AhmadGon/Advanced-Digital-Oscilloscope/Nios_SDRAM_COM/synthesis/submodules/Nios_SDRAM_COM_mm_interconnect_0_router.sv

// (C) 2001-2018 Intel Corporation. All rights reserved.
// Your use of Intel Corporation's design tools, logic functions and other 
// software and tools, and its AMPP partner logic functions, and any output 
// files from any of the foregoing (including device programming or simulation 
// files), and any associated documentation or information are expressly subject 
// to the terms and conditions of the Intel Program License Subscription 
// Agreement, Intel FPGA IP License Agreement, or other applicable 
// license agreement, including, without limitation, that your use is for the 
// sole purpose of programming logic devices manufactured by Intel and sold by 
// Intel or its authorized distributors.  Please refer to the applicable 
// agreement for further details.



// Your use of Altera Corporation's design tools, logic functions and other 
// software and tools, and its AMPP partner logic functions, and any output 
// files any of the foregoing (including device programming or simulation 
// files), and any associated documentation or information are expressly subject 
// to the terms and conditions of the Altera Program License Subscription 
// Agreement, Altera MegaCore Function License Agreement, or other applicable 
// license agreement, including, without limitation, that your use is for the 
// sole purpose of programming logic devices manufactured by Altera and sold by 
// Altera or its authorized distributors.  Please refer to the applicable 
// agreement for further details.


// $Id: //acds/rel/18.0std/ip/merlin/altera_merlin_router/altera_merlin_router.sv.terp#1 $
// $Revision: #1 $
// $Date: 2018/01/31 $
// $Author: psgswbuild $

// -------------------------------------------------------
// Merlin Router
//
// Asserts the appropriate one-hot encoded channel based on 
// either (a) the address or (b) the dest id. The DECODER_TYPE
// parameter controls this behaviour. 0 means address decoder,
// 1 means dest id decoder.
//
// In the case of (a), it also sets the destination id.
// -------------------------------------------------------

`timescale 1 ns / 1 ns

module Nios_SDRAM_COM_mm_interconnect_0_router_default_decode
  #(
     parameter DEFAULT_CHANNEL = 4,
               DEFAULT_WR_CHANNEL = -1,
               DEFAULT_RD_CHANNEL = -1,
               DEFAULT_DESTID = 5 
   )
  (output [81 - 79 : 0] default_destination_id,
   output [8-1 : 0] default_wr_channel,
   output [8-1 : 0] default_rd_channel,
   output [8-1 : 0] default_src_channel
  );

  assign default_destination_id = 
    DEFAULT_DESTID[81 - 79 : 0];

  generate
    if (DEFAULT_CHANNEL == -1) begin : no_default_channel_assignment
      assign default_src_channel = '0;
    end
    else begin : default_channel_assignment
      assign default_src_channel = 8'b1 << DEFAULT_CHANNEL;
    end
  endgenerate

  generate
    if (DEFAULT_RD_CHANNEL == -1) begin : no_default_rw_channel_assignment
      assign default_wr_channel = '0;
      assign default_rd_channel = '0;
    end
    else begin : default_rw_channel_assignment
      assign default_wr_channel = 8'b1 << DEFAULT_WR_CHANNEL;
      assign default_rd_channel = 8'b1 << DEFAULT_RD_CHANNEL;
    end
  endgenerate

endmodule


module Nios_SDRAM_COM_mm_interconnect_0_router
(
    // -------------------
    // Clock & Reset
    // -------------------
    input clk,
    input reset,

    // -------------------
    // Command Sink (Input)
    // -------------------
    input                       sink_valid,
    input  [95-1 : 0]    sink_data,
    input                       sink_startofpacket,
    input                       sink_endofpacket,
    output                      sink_ready,

    // -------------------
    // Command Source (Output)
    // -------------------
    output                          src_valid,
    output reg [95-1    : 0] src_data,
    output reg [8-1 : 0] src_channel,
    output                          src_startofpacket,
    output                          src_endofpacket,
    input                           src_ready
);

    // -------------------------------------------------------
    // Local parameters and variables
    // -------------------------------------------------------
    localparam PKT_ADDR_H = 54;
    localparam PKT_ADDR_L = 36;
    localparam PKT_DEST_ID_H = 81;
    localparam PKT_DEST_ID_L = 79;
    localparam PKT_PROTECTION_H = 85;
    localparam PKT_PROTECTION_L = 83;
    localparam ST_DATA_W = 95;
    localparam ST_CHANNEL_W = 8;
    localparam DECODER_TYPE = 0;

    localparam PKT_TRANS_WRITE = 57;
    localparam PKT_TRANS_READ  = 58;

    localparam PKT_ADDR_W = PKT_ADDR_H-PKT_ADDR_L + 1;
    localparam PKT_DEST_ID_W = PKT_DEST_ID_H-PKT_DEST_ID_L + 1;



    // -------------------------------------------------------
    // Figure out the number of bits to mask off for each slave span
    // during address decoding
    // -------------------------------------------------------
    localparam PAD0 = log2ceil(64'h40000 - 64'h20000); 
    localparam PAD1 = log2ceil(64'h41000 - 64'h40800); 
    localparam PAD2 = log2ceil(64'h41010 - 64'h41000); 
    localparam PAD3 = log2ceil(64'h41020 - 64'h41010); 
    localparam PAD4 = log2ceil(64'h41030 - 64'h41020); 
    localparam PAD5 = log2ceil(64'h41040 - 64'h41030); 
    localparam PAD6 = log2ceil(64'h41048 - 64'h41040); 
    localparam PAD7 = log2ceil(64'h41050 - 64'h41048); 
    // -------------------------------------------------------
    // Work out which address bits are significant based on the
    // address range of the slaves. If the required width is too
    // large or too small, we use the address field width instead.
    // -------------------------------------------------------
    localparam ADDR_RANGE = 64'h41050;
    localparam RANGE_ADDR_WIDTH = log2ceil(ADDR_RANGE);
    localparam OPTIMIZED_ADDR_H = (RANGE_ADDR_WIDTH > PKT_ADDR_W) ||
                                  (RANGE_ADDR_WIDTH == 0) ?
                                        PKT_ADDR_H :
                                        PKT_ADDR_L + RANGE_ADDR_WIDTH - 1;

    localparam RG = RANGE_ADDR_WIDTH-1;
    localparam REAL_ADDRESS_RANGE = OPTIMIZED_ADDR_H - PKT_ADDR_L;

      reg [PKT_ADDR_W-1 : 0] address;
      always @* begin
        address = {PKT_ADDR_W{1'b0}};
        address [REAL_ADDRESS_RANGE:0] = sink_data[OPTIMIZED_ADDR_H : PKT_ADDR_L];
      end   

    // -------------------------------------------------------
    // Pass almost everything through, untouched
    // -------------------------------------------------------
    assign sink_ready        = src_ready;
    assign src_valid         = sink_valid;
    assign src_startofpacket = sink_startofpacket;
    assign src_endofpacket   = sink_endofpacket;
    wire [PKT_DEST_ID_W-1:0] default_destid;
    wire [8-1 : 0] default_src_channel;




    // -------------------------------------------------------
    // Write and read transaction signals
    // -------------------------------------------------------
    wire read_transaction;
    assign read_transaction  = sink_data[PKT_TRANS_READ];


    Nios_SDRAM_COM_mm_interconnect_0_router_default_decode the_default_decode(
      .default_destination_id (default_destid),
      .default_wr_channel   (),
      .default_rd_channel   (),
      .default_src_channel  (default_src_channel)
    );

    always @* begin
        src_data    = sink_data;
        src_channel = default_src_channel;
        src_data[PKT_DEST_ID_H:PKT_DEST_ID_L] = default_destid;

        // --------------------------------------------------
        // Address Decoder
        // Sets the channel and destination ID based on the address
        // --------------------------------------------------

    // ( 0x20000 .. 0x40000 )
    if ( {address[RG:PAD0],{PAD0{1'b0}}} == 19'h20000   ) begin
            src_channel = 8'b00010000;
            src_data[PKT_DEST_ID_H:PKT_DEST_ID_L] = 5;
    end

    // ( 0x40800 .. 0x41000 )
    if ( {address[RG:PAD1],{PAD1{1'b0}}} == 19'h40800   ) begin
            src_channel = 8'b00000100;
            src_data[PKT_DEST_ID_H:PKT_DEST_ID_L] = 4;
    end

    // ( 0x41000 .. 0x41010 )
    if ( {address[RG:PAD2],{PAD2{1'b0}}} == 19'h41000   ) begin
            src_channel = 8'b00001000;
            src_data[PKT_DEST_ID_H:PKT_DEST_ID_L] = 6;
    end

    // ( 0x41010 .. 0x41020 )
    if ( {address[RG:PAD3],{PAD3{1'b0}}} == 19'h41010  && read_transaction  ) begin
            src_channel = 8'b10000000;
            src_data[PKT_DEST_ID_H:PKT_DEST_ID_L] = 2;
    end

    // ( 0x41020 .. 0x41030 )
    if ( {address[RG:PAD4],{PAD4{1'b0}}} == 19'h41020   ) begin
            src_channel = 8'b01000000;
            src_data[PKT_DEST_ID_H:PKT_DEST_ID_L] = 0;
    end

    // ( 0x41030 .. 0x41040 )
    if ( {address[RG:PAD5],{PAD5{1'b0}}} == 19'h41030  && read_transaction  ) begin
            src_channel = 8'b00100000;
            src_data[PKT_DEST_ID_H:PKT_DEST_ID_L] = 1;
    end

    // ( 0x41040 .. 0x41048 )
    if ( {address[RG:PAD6],{PAD6{1'b0}}} == 19'h41040  && read_transaction  ) begin
            src_channel = 8'b00000010;
            src_data[PKT_DEST_ID_H:PKT_DEST_ID_L] = 7;
    end

    // ( 0x41048 .. 0x41050 )
    if ( {address[RG:PAD7],{PAD7{1'b0}}} == 19'h41048   ) begin
            src_channel = 8'b00000001;
            src_data[PKT_DEST_ID_H:PKT_DEST_ID_L] = 3;
    end

end


    // --------------------------------------------------
    // Ceil(log2()) function
    // --------------------------------------------------
    function integer log2ceil;
        input reg[65:0] val;
        reg [65:0] i;

        begin
            i = 1;
            log2ceil = 0;

            while (i < val) begin
                log2ceil = log2ceil + 1;
                i = i << 1;
            end
        end
    endfunction

endmodule
