AhmadGon/Advanced-Digital-Oscilloscope/Fraction_BCD_LUT.v

//================================================================
//     Fraction BCD LUT Module
//		 
//		 This module is for fraction part of the floating point value
//		 expressed as BCD Look-Up table 
//================================================================
module Fraction_BCD_LUT(
	input Main_CLK,
	input [7:0] Exponent,
	input [31:0] Fraction_Binary,
	output reg [7:0] Fraction_BCD
);
always @(Main_CLK)
	begin
	if (Exponent >= 127)
		begin
		case(Fraction_Binary)
		0: Fraction_BCD <= 0; 
		1: Fraction_BCD <= 0; 
		2: Fraction_BCD <= 1; 
		3: Fraction_BCD <= 1; 
		4: Fraction_BCD <= 2; 
		5: Fraction_BCD <= 2; 
		6: Fraction_BCD <= 2; 
		7: Fraction_BCD <= 3; 
		8: Fraction_BCD <= 3; 
		9: Fraction_BCD <= 4; 
		10: Fraction_BCD <= 4; 
		11: Fraction_BCD <= 4; 
		12: Fraction_BCD <= 5; 
		13: Fraction_BCD <= 5; 
		14: Fraction_BCD <= 5; 
		15: Fraction_BCD <= 6; 
		16: Fraction_BCD <= 6; 
		17: Fraction_BCD <= 7; 
		18: Fraction_BCD <= 7; 
		19: Fraction_BCD <= 7; 
		20: Fraction_BCD <= 8; 
		21: Fraction_BCD <= 8; 
		22: Fraction_BCD <= 9; 
		23: Fraction_BCD <= 9; 
		24: Fraction_BCD <= 9; 
		25: Fraction_BCD <= 16; 
		26: Fraction_BCD <= 16; 
		27: Fraction_BCD <= 17; 
		28: Fraction_BCD <= 17; 
		29: Fraction_BCD <= 17; 
		30: Fraction_BCD <= 18; 
		31: Fraction_BCD <= 18; 
		32: Fraction_BCD <= 19; 
		33: Fraction_BCD <= 19; 
		34: Fraction_BCD <= 19; 
		35: Fraction_BCD <= 20; 
		36: Fraction_BCD <= 20; 
		37: Fraction_BCD <= 20; 
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
		247: Fraction_BCD <= 228; 
		248: Fraction_BCD <= 240; 
		249: Fraction_BCD <= 246; 
		250: Fraction_BCD <= 259; 
		251: Fraction_BCD <= 265; 
		252: Fraction_BCD <= 277; 
		253: Fraction_BCD <= 289; 
		254: Fraction_BCD <= 296;
		default: Fraction_BCD <= 0;
		endcase
		end
	end
endmodule 
