AhmadGon/Advanced-Digital-Oscilloscope/Nios_SDRAM_COM/Nios_SDRAM_COM_inst.v

	Nios_SDRAM_COM u0 (
		.clk_clk                  (<connected-to-clk_clk>),                  //                  clk.clk
		.events_export            (<connected-to-events_export>),            //               events.export
		.input_data_export        (<connected-to-input_data_export>),        //           input_data.export
		.output_address_export    (<connected-to-output_address_export>),    //       output_address.export
		.reset_reset_n            (<connected-to-reset_reset_n>),            //                reset.reset_n
		.clock_bridge_out_clk_clk (<connected-to-clock_bridge_out_clk_clk>)  // clock_bridge_out_clk.clk
	);
